LMWB/Fettuccine-Alfredo/Spice/cc_driver_led.asc

D1: LED; NSCW100
D2: LED; NSCW100
D3: diode; 1N4148
D4: diode; 1N4148
D5: diode; 1N4148
D6: LED; NSCW100
D7: LED; NSCW100
D8: LED; NSCW100
D9: LED; NSCW100
Q1: npn; 2N3904
R2: res; 10k
R3: res; 100
V1: voltage; 24
Named nets: 0, Vcc, X2
Current Sink
.tran 100m
.dc V1 24 5 1
